lhr-solar/Power-Generation-Curve-Tracer/BPS/Master/BPSMaster.sch

## KiCad design BPS/Master/BPSMaster.sch (2020-01-25)

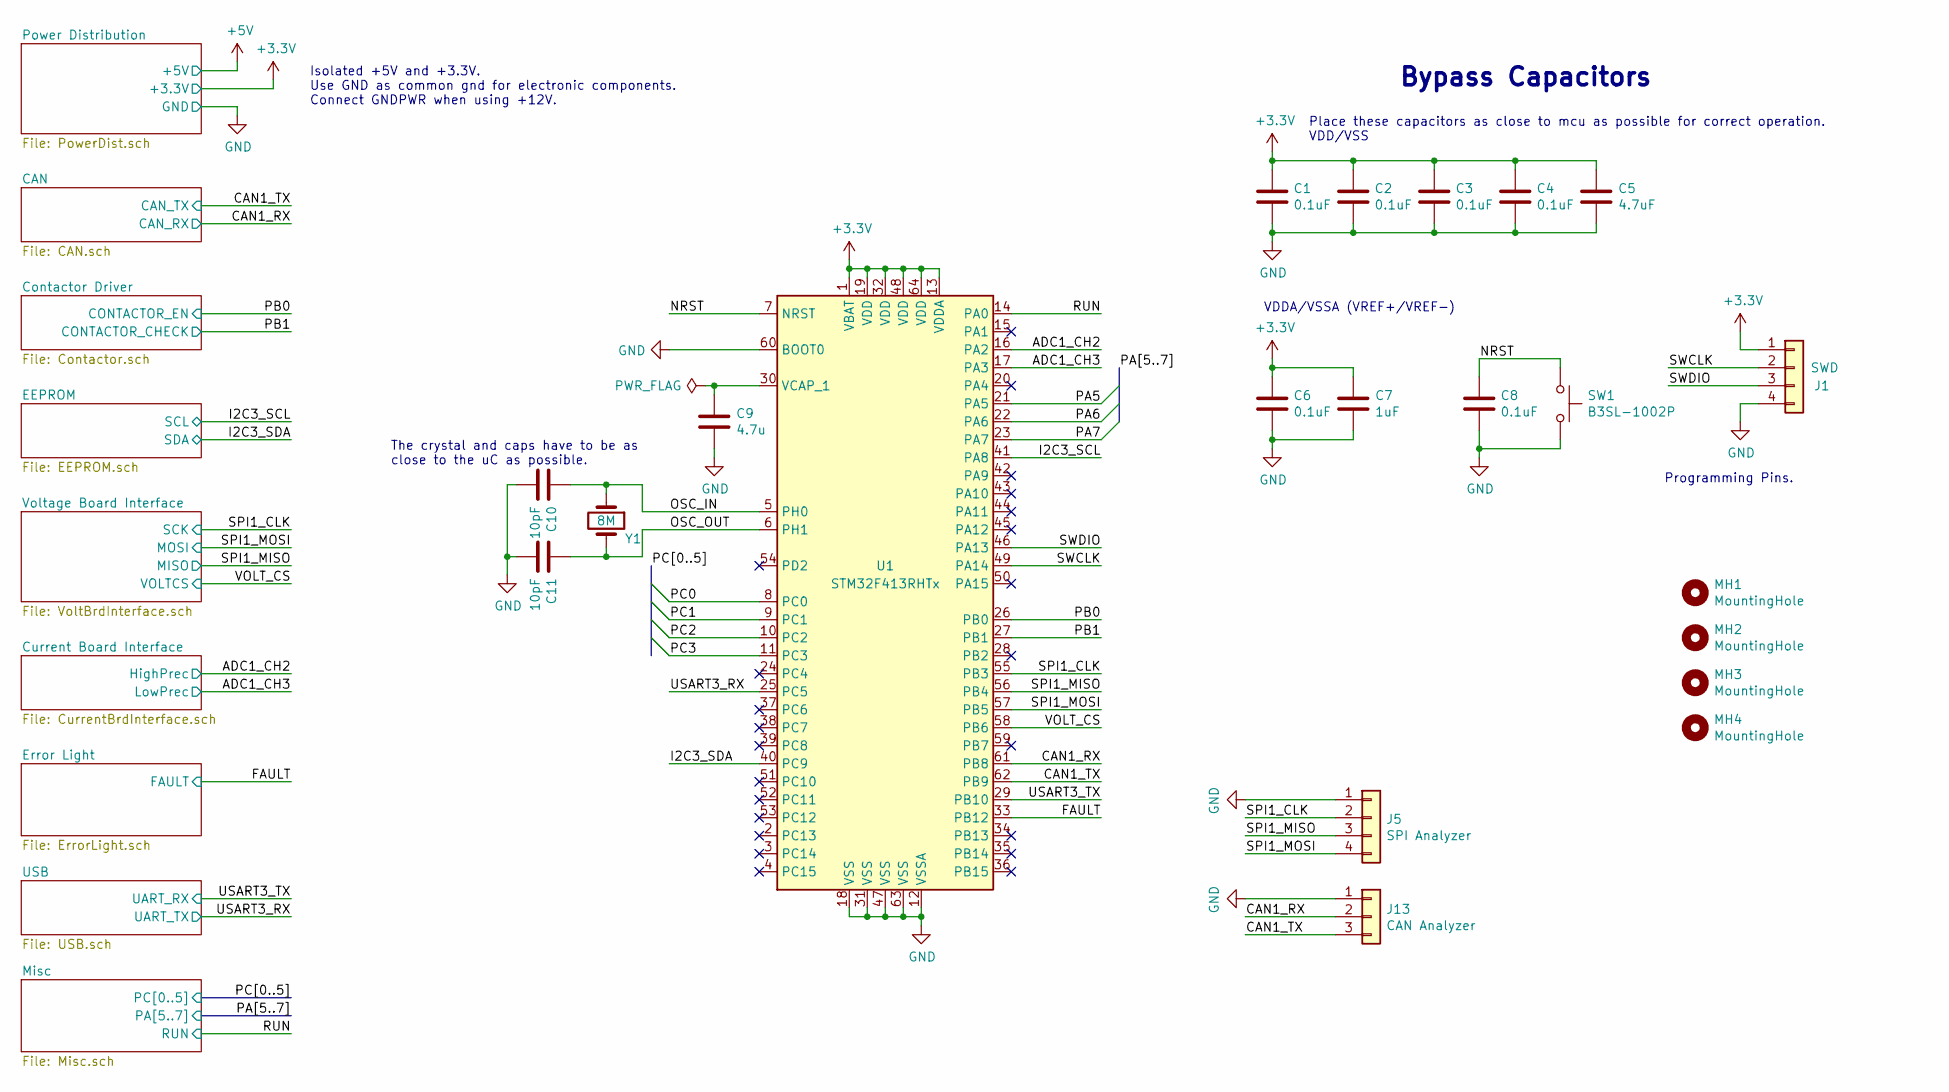
[picture p58: schematic BPSMaster.sch]

Parts:
C1, C2, C3, C4, C6, C8: 0.1uF; C_0805_2012Metric
C5: 4.7uF; C_0805_2012Metric
C7: 1uF; C_0805_2012Metric
C9: 4.7u; C_0805_2012Metric
C10, C11: 10pF; C_0805_2012Metric
J1: SWD; PinHeader_1x04_P2.54mm_Vertical
J5: SPI Analyzer; PinHeader_1x04_P2.54mm_Vertical
J13: CAN Analyzer; PinHeader_1x03_P2.54mm_Vertical
MH1, MH2, MH3, MH4: MountingHole; MountingHole_3mm
SW1: B3SL-1002P; SW_SPST_B3SL-1002P
U1: STM32F413RHTx; LQFP-64_10x10mm_P0.5mm
Y1: 8M; Crystal_SMD_TXC_7A-2Pin_5x3.2mm

Connections:
+3.3V: C1.1, C2.1, C3.1, C4.1, C5.1, C6.1, C7.1, J1.1, U1.1 (VBAT), U1.13 (VDDA), U1.19 (VDD), U1.32 (VDD), U1.48 (VDD), U1.64 (VDD)
ADC1_CH2: U1.16 (PA2)
ADC1_CH3: U1.17 (PA3)
CAN1_RX: J13.2, U1.61 (PB8)
CAN1_TX: J13.3, U1.62 (PB9)
FAULT: U1.33 (PB12)
GND: C1.2, C2.2, C3.2, C4.2, C5.2, C6.2, C7.2, C8.2, C9.2, C10.2, C11.2, J1.4, J5.1, J13.1, SW1.2, U1.12 (VSSA), U1.18 (VSS), U1.31 (VSS), U1.47 (VSS), U1.60 (BOOT0), U1.63 (VSS)
I2C3_SCL: U1.41 (PA8)
I2C3_SDA: U1.40 (PC9)
NRST: C8.1, SW1.1, U1.7 (NRST)
unnamed: C9.1, U1.30 (VCAP_1)
OSC_IN: C10.1, U1.5 (PH0), Y1.1
OSC_OUT: C11.1, U1.6 (PH1), Y1.2
PA5: U1.21 (PA5)
PA6: U1.22 (PA6)
PA7: U1.23 (PA7)
PB0: U1.26 (PB0)
PB1: U1.27 (PB1)
PC0: U1.8 (PC0)
PC1: U1.9 (PC1)
PC2: U1.10 (PC2)
PC3: U1.11 (PC3)
RUN: U1.14 (PA0)
SPI1_CLK: J5.2, U1.55 (PB3)
SPI1_MISO: J5.3, U1.56 (PB4)
SPI1_MOSI: J5.4, U1.57 (PB5)
SWCLK: J1.2, U1.49 (PA14)
SWDIO: J1.3, U1.46 (PA13)
USART3_RX: U1.25 (PC5)
USART3_TX: U1.29 (PB10)
VOLT_CS: U1.58 (PB6)

Notes on the sheet:
Place these capacitors as close to mcu as possible for correct operation. VDD/VSS
VDDA/VSSA (VREF+/VREF-)
Isolated +5V and +3.3V. Use GND as common gnd for electronic components. Connect GNDPWR when using +12V.
The crystal and caps have to be as close to the uC as possible.
Programming Pins.
Bypass Capacitors
