lhr-solar/Power-Generation-Curve-Tracer/BPS/Master/CAN.sch

## KiCad design BPS/Master/CAN.sch (2020-01-25)

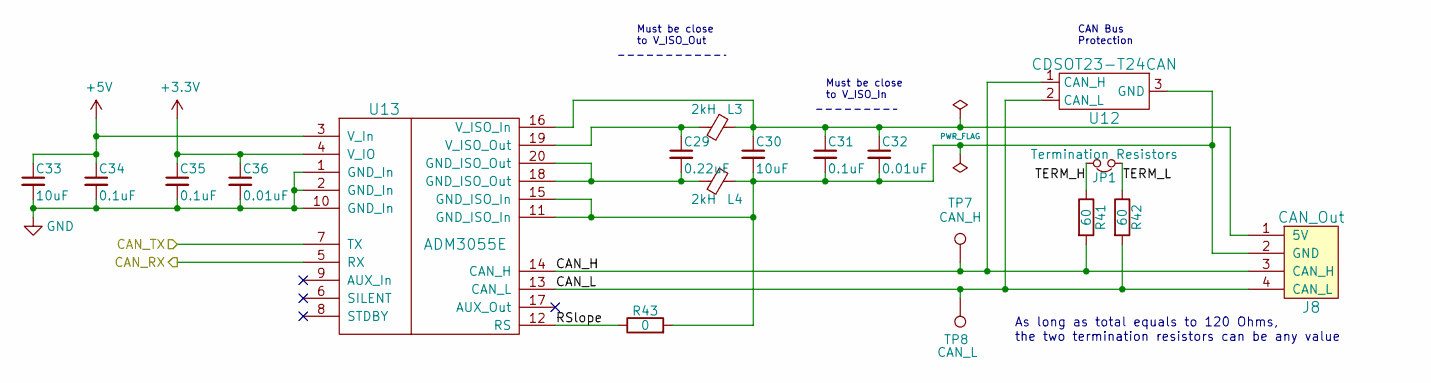
[picture p59: schematic CAN.sch]

Parts:
C29: 0.22uF; C_0805_2012Metric
C30, C33: 10uF; C_0805_2012Metric
C31, C34, C35: 0.1uF; C_0805_2012Metric
C32, C36: 0.01uF; C_0805_2012Metric
J8: CAN_Out; Molex_MicroFit3.0_1x4xP3.00mm_PolarizingPeg_Vertical
JP1: Termination Resistors; PinHeader_1x02_P2.54mm_Vertical
L3, L4: 2kH; L_0805_2012Metric
R41, R42: 60; R_0805_2012Metric
R43: 0; R_0805_2012Metric
TP7: CAN_H; TestPoint_Keystone_5005-5009_Compact
TP8: CAN_L; TestPoint_Keystone_5005-5009_Compact
U12: CDSOT23-T24CAN; SOT-23W
U13: ADM3055E; SOIC-20W_7.5x15.4mm_Pitch1.27mm

Connections:
+3.3V: C35.1, C36.1, U13.4 (V_IO)
+5V: C33.1, C34.1, U13.3 (V_In)
CAN_H: J8.3 (CAN_H), R41.2, TP7.1, U12.1 (CAN_H), U13.14 (CAN_H)
CAN_L: J8.4 (CAN_L), R42.2, TP8.1, U12.2 (CAN_L), U13.13 (CAN_L)
CAN_RX: U13.5 (RX)
CAN_TX: U13.7 (TX)
GND: C33.2, C34.2, C35.2, C36.2, U13.1 (GND_In), U13.2 (GND_In), U13.10 (GND_In)
unnamed: C29.1, L3.2, U13.19 (V_ISO_Out)
unnamed: C29.2, L4.2, U13.18 (GND_ISO_Out), U13.20 (GND_ISO_Out)
unnamed: C30.1, C31.1, C32.1, J8.1 (5V), L3.1, U13.16 (V_ISO_In)
unnamed: C30.2, C31.2, C32.2, J8.2 (GND), L4.1, R43.2, U12.3 (GND), U13.11 (GND_ISO_In), U13.15 (GND_ISO_In)
RSlope: R43.1, U13.12 (RS)
TERM_H: JP1.2, R41.1
TERM_L: JP1.1, R42.1

Notes on the sheet:
Must be close to V_ISO_Out
Must be close to V_ISO_In
CAN Bus Protection
As long as total equals to 120 Ohms, the two termination resistors can be any value
