lhr-solar/Power-Generation-Curve-Tracer/BPS/Master/EEPROM.sch

## KiCad design BPS/Master/EEPROM.sch (2020-01-25)

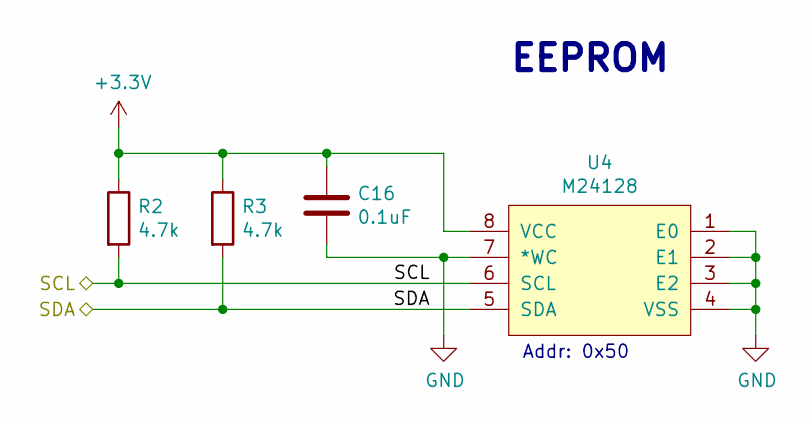
[picture p60: schematic EEPROM.sch]

Parts:
C16: 0.1uF; C_0805_2012Metric
R2, R3: 4.7k; R_0805_2012Metric
U4: M24128; M24128-BRMN6P

Connections:
+3.3V: C16.1, R2.1, R3.1, U4.8 (VCC)
GND: C16.2, U4.1 (E0), U4.2 (E1), U4.3 (E2), U4.4 (VSS), U4.7 (*WC)
SCL: R2.2, U4.6 (SCL)
SDA: R3.2, U4.5 (SDA)

Notes on the sheet:
EEPROM
Addr: 0x50
