lhr-solar/Power-Generation-Curve-Tracer/BPS/Master/I2C.sch

## KiCad design BPS/Master/I2C.sch (2019-02-07)

Schematic: I2C.sch

Parts:
C31: 0.1uF; C_0805_2012Metric
J14: Conn_01x03; PinHeader_1x02_P2.54mm_Vertical
R13, R14: 4.7k; R_0805_2012Metric
U8: M24128; M24128-BRMN6P

Notes on the sheet:
EEPROM
Addr: 0x50
