lhr-solar/Power-Generation-Curve-Tracer/BPS/Master/Misc.sch

## KiCad design BPS/Master/Misc.sch (2020-01-25)

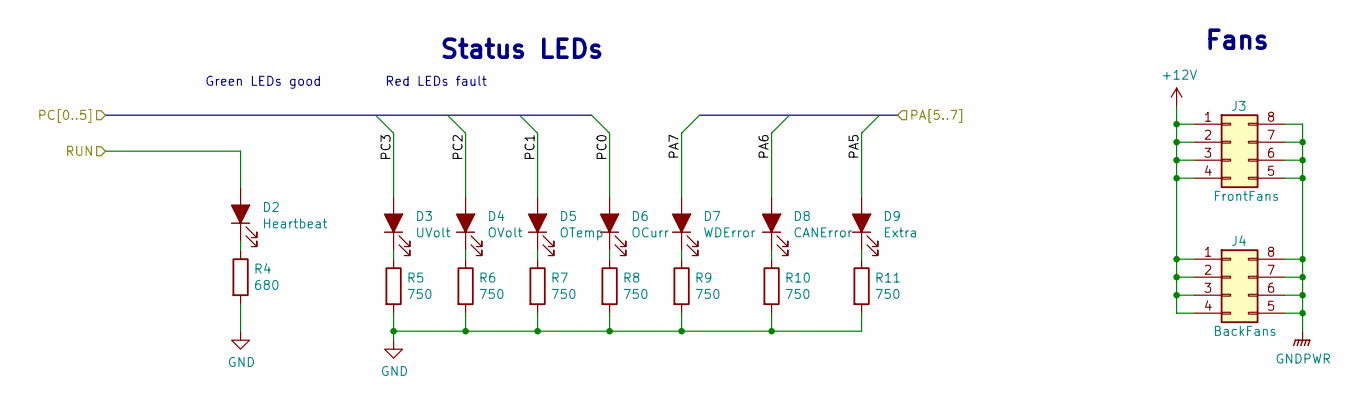
[picture p61: schematic Misc.sch]

Parts:
D2: Heartbeat; LED_0805_2012Metric
D3: UVolt; LED_0805_2012Metric
D4: OVolt; LED_0805_2012Metric
D5: OTemp; LED_0805_2012Metric
D6: OCurr; LED_0805_2012Metric
D7: WDError; LED_0805_2012Metric
D8: CANError; LED_0805_2012Metric
D9: Extra; LED_0805_2012Metric
J3: FrontFans; Molex_MicroFit3.0_2x4xP3.00mm_PolarizingPeg_Vertical
J4: BackFans; Molex_MicroFit3.0_2x4xP3.00mm_PolarizingPeg_Vertical
R4: 680; R_0805_2012Metric
R5, R6, R7, R8, R9, R10, R11: 750; R_0805_2012Metric

Connections:
+12V: J3.1, J3.2, J3.3, J3.4, J4.1, J4.2, J4.3, J4.4
GND: R4.2, R5.2, R6.2, R7.2, R8.2, R9.2, R10.2, R11.2
GNDPWR: J3.5, J3.6, J3.7, J3.8, J4.5, J4.6, J4.7, J4.8
unnamed: D2.1 (K), R4.1
unnamed: D3.1 (K), R5.1
unnamed: D4.1 (K), R6.1
unnamed: D5.1 (K), R7.1
unnamed: D6.1 (K), R8.1
unnamed: D7.1 (K), R9.1
unnamed: D8.1 (K), R10.1
unnamed: D9.1 (K), R11.1
PA5: D9.2 (A)
PA6: D8.2 (A)
PA7: D7.2 (A)
PC0: D6.2 (A)
PC1: D5.2 (A)
PC2: D4.2 (A)
PC3: D3.2 (A)
RUN: D2.2 (A)

Notes on the sheet:
Fans
Green LEDs good
Red LEDs fault
Status LEDs
