lhr-solar/Power-Generation-Curve-Tracer/BPS/Master/USB.sch

## KiCad design BPS/Master/USB.sch (2020-01-25)

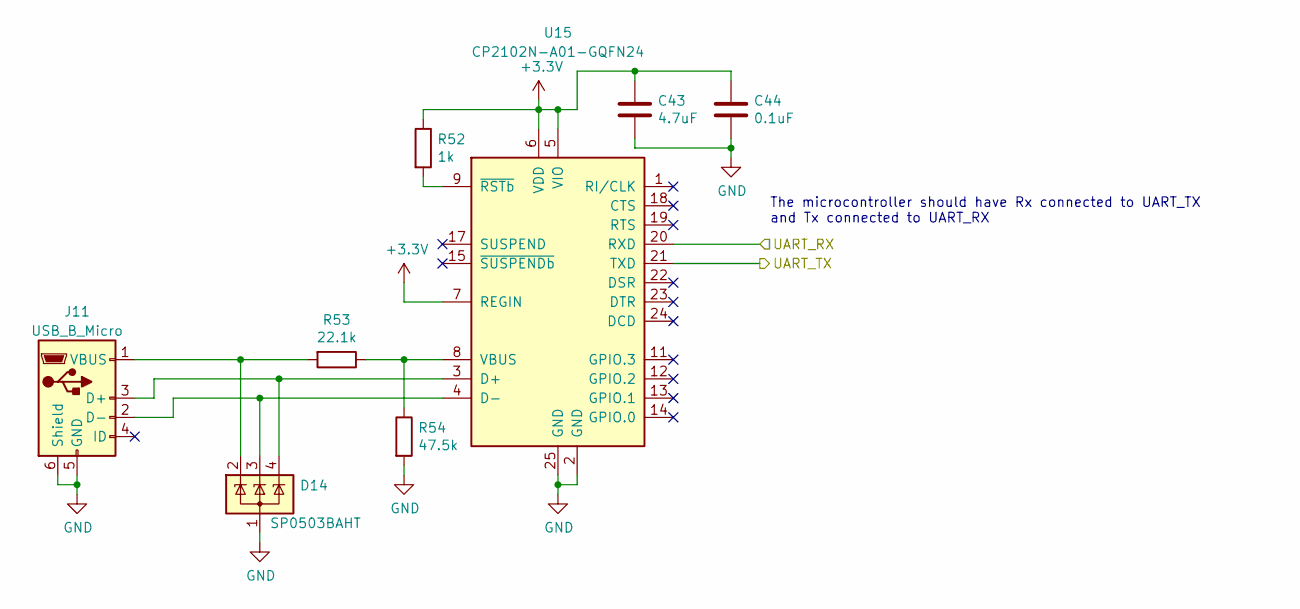
[picture p62: schematic USB.sch]

Parts:
C43: 4.7uF; C_0805_2012Metric
C44: 0.1uF; C_0805_2012Metric
D14: SP0503BAHT; SOT-143
J11: USB_B_Micro; USB_Micro-B_Molex-105017-0001
R52: 1k; R_0805_2012Metric
R53: 22.1k; R_0805_2012Metric
R54: 47.5k; R_0805_2012Metric
U15: CP2102N-A01-GQFN24; QFN-24-1EP_4x4mm_P0.5mm_EP2.6x2.6mm

Connections:
+3.3V: C43.1, C44.1, R52.1, U15.5 (VIO), U15.6 (VDD), U15.7 (REGIN)
GND: C43.2, C44.2, D14.1 (A), J11.5 (GND), J11.6 (Shield), R54.2, U15.2 (GND), U15.25 (GND)
unnamed: D14.2 (K), J11.1 (VBUS), R53.2
unnamed: D14.3 (K), J11.2 (D-), U15.4 (D-)
unnamed: D14.4 (K), J11.3 (D+), U15.3 (D+)
unnamed: R52.2, U15.9 (~RSTb)
unnamed: R53.1, R54.1, U15.8 (VBUS)
UART_RX: U15.20 (RXD)
UART_TX: U15.21 (TXD)

Notes on the sheet:
The microcontroller should have Rx connected to UART_TX and Tx connected to UART_RX
