lhr-solar/Power-Generation-Curve-Tracer/BPS/Debugger/Debugger/Debugger.sch

## KiCad design BPS/Debugger/Debugger/Debugger.sch (2019-02-19)

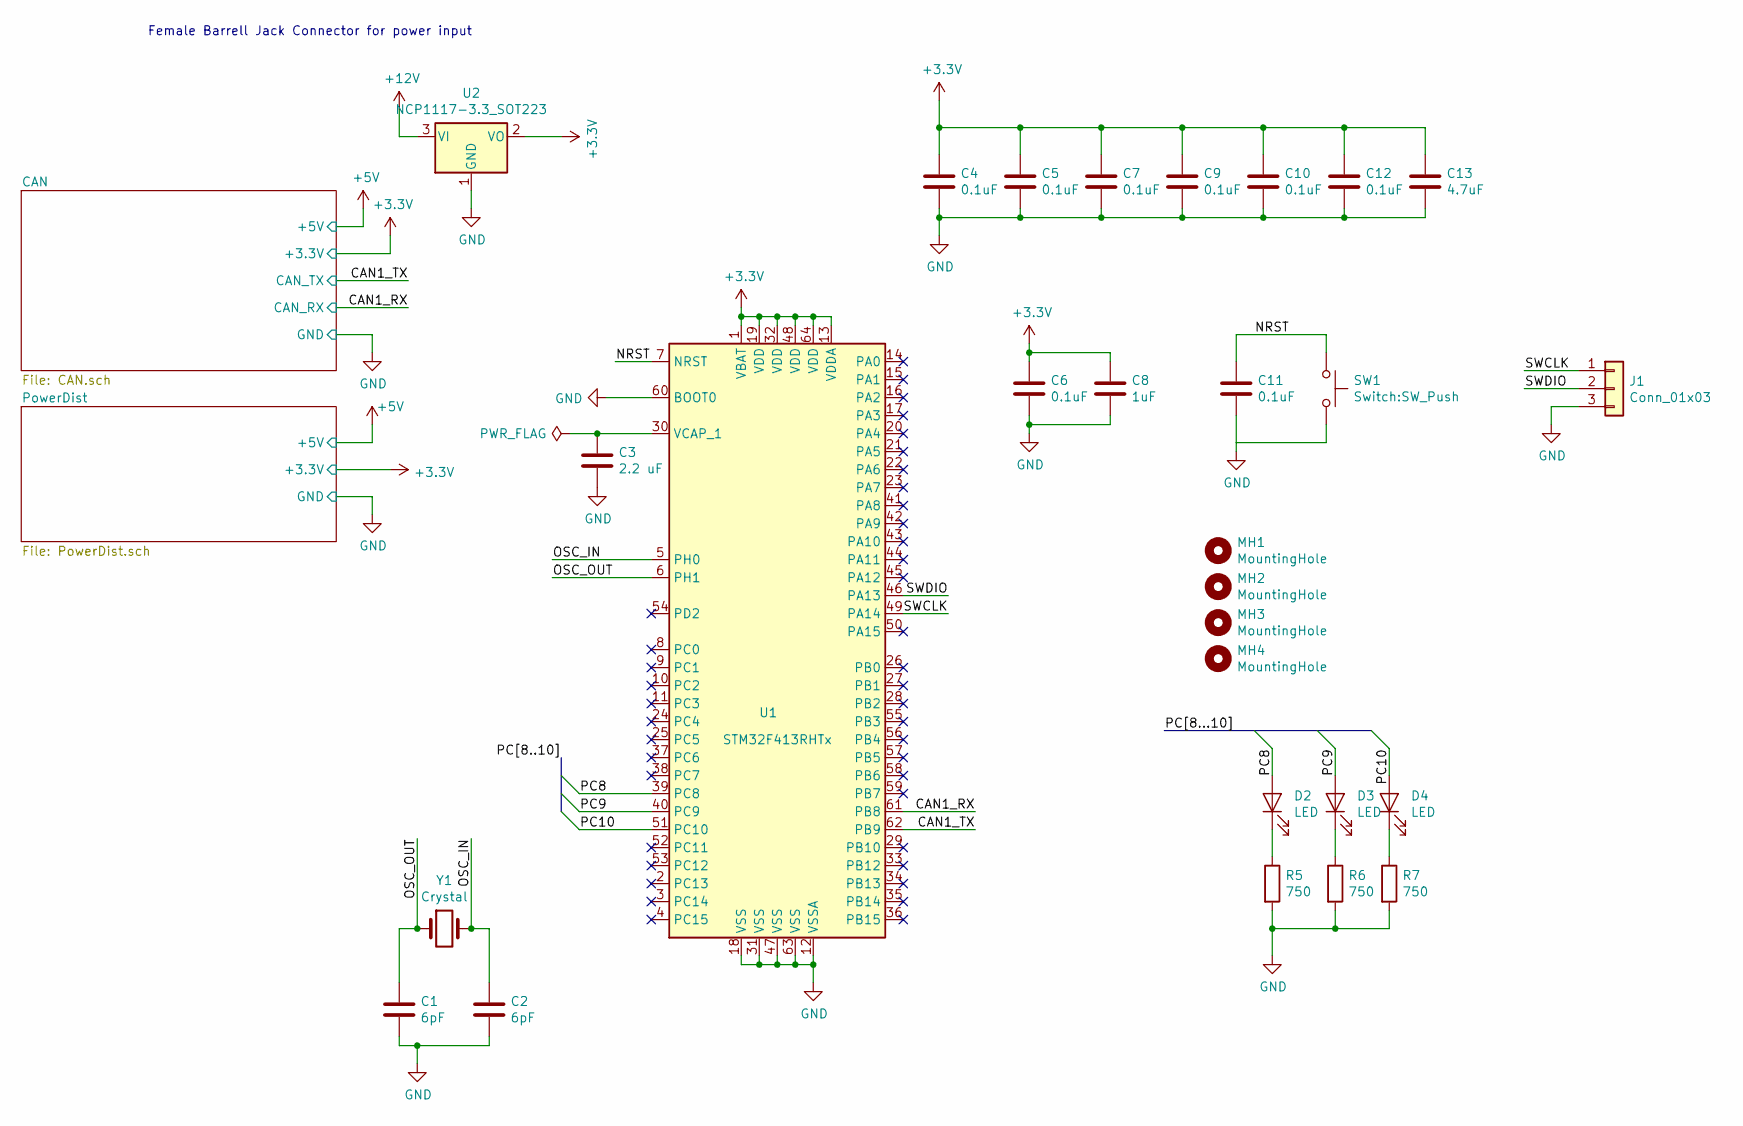
[picture p63: schematic Debugger.sch]

Parts:
C1, C2: 6pF; C_0805_2012Metric
C3: 2.2 uF; C_0805_2012Metric
C4, C5, C6, C7, C9, C10, C11, C12: 0.1uF; C_0805_2012Metric
C8: 1uF; C_0805_2012Metric
C13: 4.7uF; C_0805_2012Metric
D2, D3, D4: LED; LED_0805_2012Metric
J1: Conn_01x03; PinHeader_1x02_P2.54mm_Vertical
MH1, MH2, MH3, MH4: MountingHole; MountingHole_3mm
R5, R6, R7: 750; R_0805_2012Metric
SW1: Switch:SW_Push; SW_SPST_B3SL-1002P
U1: STM32F413RHTx; LQFP-64_10x10mm_P0.5mm
U2: NCP1117-3.3_SOT223; SOT-223-3_TabPin2
Y1: Crystal; NX8045GB-8.000M-STD-CSJ-1

Connections:
+3.3V: C4.1, C5.1, C6.1, C7.1, C8.1, C9.1, C10.1, C12.1, C13.1, U1.1 (VBAT), U1.13 (VDDA), U1.19 (VDD), U1.32 (VDD), U1.48 (VDD), U1.64 (VDD), U2.2 (VO)
+12V: U2.3 (VI)
CAN1_RX: U1.61 (PB8)
CAN1_TX: U1.62 (PB9)
GND: C1.2, C2.2, C3.2, C4.2, C5.2, C6.2, C7.2, C8.2, C9.2, C10.2, C11.2, C12.2, C13.2, J1.3, R5.2, R6.2, R7.2, SW1.2, U1.12 (VSSA), U1.18 (VSS), U1.31 (VSS), U1.47 (VSS), U1.60 (BOOT0), U1.63 (VSS), U2.1 (GND)
NRST: C11.1, SW1.1, U1.7 (NRST)
unnamed: C3.1, U1.30 (VCAP_1)
unnamed: D2.1 (K), R5.1
unnamed: D3.1 (K), R6.1
unnamed: D4.1 (K), R7.1
OSC_IN: C2.1, U1.5 (PH0), Y1.2
OSC_OUT: C1.1, U1.6 (PH1), Y1.1
PC8: D2.2 (A), U1.39 (PC8)
PC9: D3.2 (A), U1.40 (PC9)
PC10: D4.2 (A), U1.51 (PC10)
SWCLK: J1.1, U1.49 (PA14)
SWDIO: J1.2, U1.46 (PA13)

Notes on the sheet:
Female Barrell Jack Connector for power input
