lhr-solar/Power-Generation-Curve-Tracer/BPS/Debugger/Debugger/PowerDist.sch

## KiCad design BPS/Debugger/Debugger/PowerDist.sch (2019-02-19)

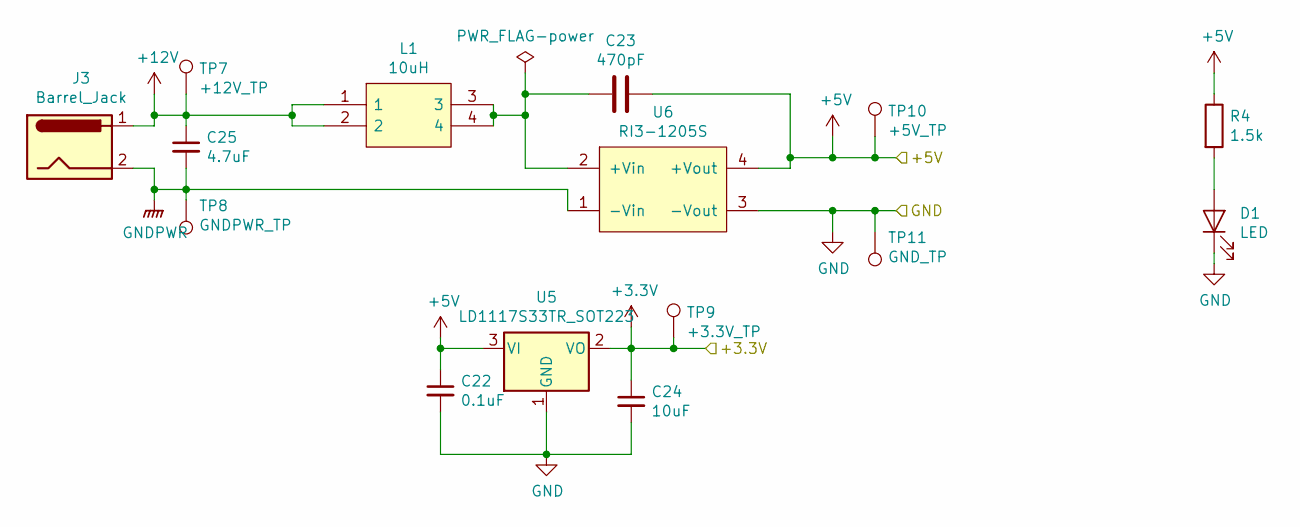
[picture p64: schematic PowerDist.sch]

Parts:
C22: 0.1uF; C_0805_2012Metric
C23: 470pF; C_2220_5650Metric
C24: 10uF; C_0805_2012Metric
C25: 4.7uF; C_0805_2012Metric
D1: LED; LED_0805_2012Metric
J3: Barrel_Jack; BarrelJack_Horizontal
L1: 10uH; SRF0905A; Mouser Part Number 652-SRF0905-100Y
R4: 1.5k; R_0805_2012Metric
TP7: +12V_TP; TestPoint_Keystone_5005-5009_Compact
TP8: GNDPWR_TP; TestPoint_Keystone_5005-5009_Compact
TP9: +3.3V_TP; TestPoint_Keystone_5005-5009_Compact
TP10: +5V_TP; TestPoint_Keystone_5005-5009_Compact
TP11: GND_TP; TestPoint_Keystone_5005-5009_Compact
U5: LD1117S33TR_SOT223; SOT-223-3_TabPin2
U6: RI3-1205S; RI3_DC_Converter

Connections:
+3.3V: C24.1, TP9.1, U5.2 (VO)
+5V: C22.1, C23.1, R4.1, TP10.1, U5.3 (VI), U6.4 (+Vout)
+12V: C25.1, J3.1, L1.1, L1.2, TP7.1
GND: C22.2, C24.2, D1.1 (K), TP11.1, U5.1 (GND), U6.3 (-Vout)
GNDPWR: C25.2, J3.2, TP8.1, U6.1 (-Vin)
unnamed: C23.2, L1.3, L1.4, U6.2 (+Vin)
unnamed: D1.2 (A), R4.2
