lhr-solar/Power-Generation-Curve-Tracer/BPS/Debugger/Debugger/file5C5F7A4C.sch

## KiCad design BPS/Debugger/Debugger/file5C5F7A4C.sch (2019-02-16)

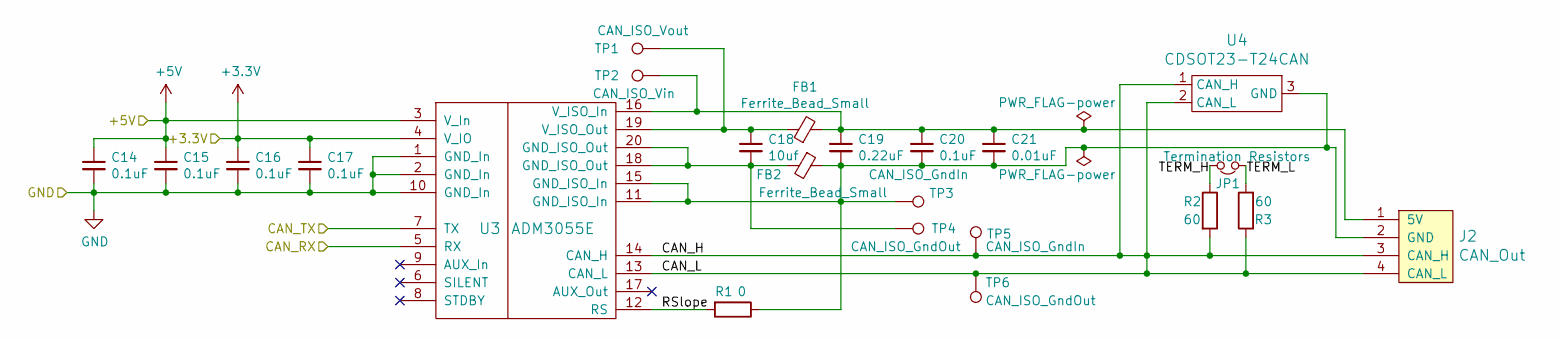
[picture p65: schematic file5C5F7A4C.sch]

Parts:
C14, C15, C16, C17, C20: 0.1uF
C18: 10uf
C19: 0.22uF
C21: 0.01uF
FB1, FB2: Ferrite_Bead_Small
J2: CAN_Out
JP1: Termination Resistors
R1: 0
R2, R3: 60
TP1: CAN_ISO_Vout
TP2: CAN_ISO_Vin
TP3, TP5: CAN_ISO_GndIn
TP4, TP6: CAN_ISO_GndOut
U3: ADM3055E
U4: CDSOT23-T24CAN

Connections:
+3.3V: C16.1, C17.1, U3.4 (V_IO)
+5V: C14.1, C15.1, U3.3 (V_In)
CAN_H: J2.3 (CAN_H), J2.4 (CAN_L), R2.2, R3.1, TP5.1, TP6.1, U3.13 (CAN_L), U3.14 (CAN_H), U4.1 (CAN_H), U4.2 (CAN_L)
CAN_RX: U3.5 (RX)
CAN_TX: U3.7 (TX)
GND: C14.2, C15.2, C16.2, C17.2, U3.1 (GND_In), U3.2 (GND_In), U3.10 (GND_In)
unnamed: C18.1, FB1.1, TP1.1, U3.19 (V_ISO_Out)
unnamed: C18.2, FB2.2, TP4.1, U3.18 (GND_ISO_Out), U3.20 (GND_ISO_Out)
unnamed: C19.1, C20.1, C21.1, FB1.2, J2.1 (5V), TP2.1, U3.16 (V_ISO_In)
unnamed: C19.2, C20.2, C21.2, FB2.1, J2.2 (GND), R1.1, TP3.1, U3.11 (GND_ISO_In), U3.15 (GND_ISO_In), U4.3 (GND)
RSlope: R1.2, U3.12 (RS)
TERM_H: JP1.2, R2.1
TERM_L: JP1.1, R3.2
